a-oleksak/Bio-impedance-Sensing/code/bluetooth_test_seniorDesign.ino

// -----------------------------------------------------------------------------------------
// Bluetooth Test
// Components: HC-05 Bluetooth module, Arduino Uno
//
// This code uses the built in LED on the Arduino Uno to introduce the functionality
// of the bluetooth module.
//
// Note: Upload code to the Arduino without the module connected, connect the bluetooth 
// module and power the Arduino. Pair the HC-05 to your computer and assign the COM port
// in the Arduino IDE.
// -----------------------------------------------------------------------------------------

void setup() {
  Serial.begin(9600);
  pinMode(LED_BUILTIN, OUTPUT);
  
  Serial.println("=== Bluetooth Remote Control ===");
  Serial.println("Commands:");
  Serial.println("  '1' - Turn LED ON");
  Serial.println("  '0' - Turn LED OFF");
  Serial.println("  'b' - Blink LED 5 times");
}

void loop() {
  if(Serial.available()) {
    char cmd = Serial.read();
    
    switch(cmd) {
      case '1':
        digitalWrite(LED_BUILTIN, HIGH);
        Serial.println("LED ON");
        break;
        
      case '0':
        digitalWrite(LED_BUILTIN, LOW);
        Serial.println("LED OFF");
        break;
        
      case 'b':
        Serial.println("Blinking LED 5 times...");
        for(int i = 0; i < 5; i++) {
          digitalWrite(LED_BUILTIN, HIGH);
          delay(200);
          digitalWrite(LED_BUILTIN, LOW);
          delay(200);
        }
        Serial.println("\n Blink complete!");
        break;
        
      default:
        Serial.print("Unknown");
    }
  }
}
